antmicro/com-express-7-baseboard/assets/previews/layer1.png

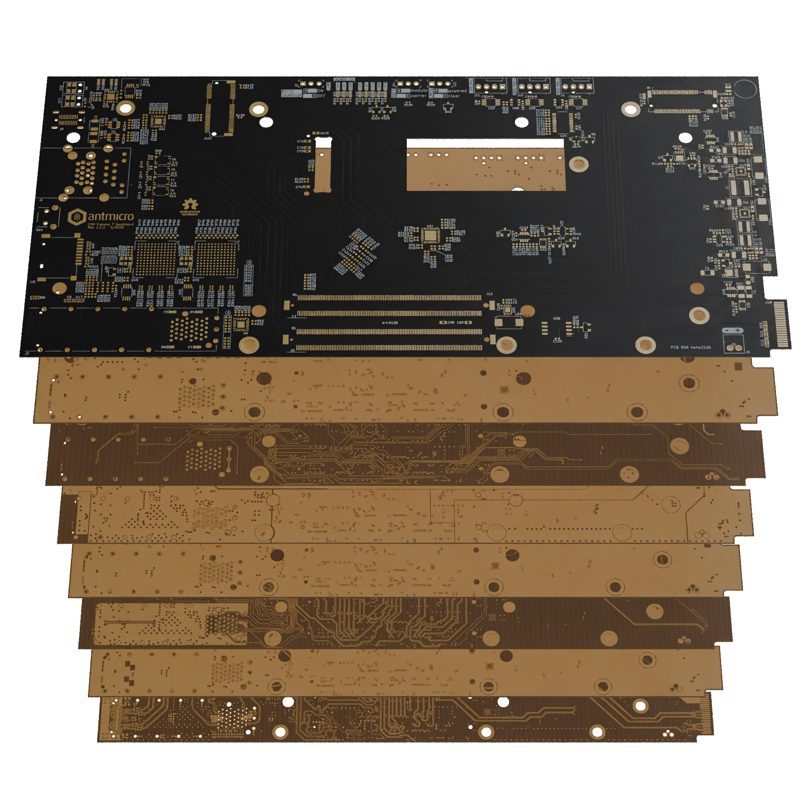
assets/previews/layer1.png
