antmicro/com-express-7-baseboard/assets/previews/layer2.png

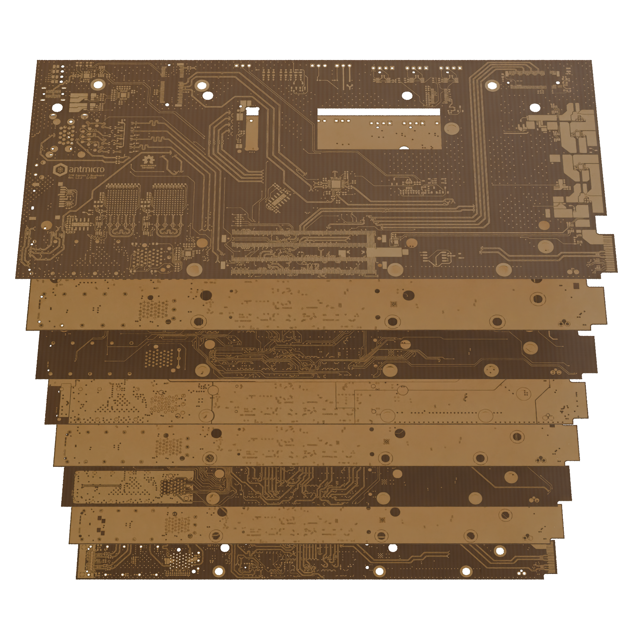
assets/previews/layer2.png
