antmicro/com-express-7-baseboard/assets/previews/layer2.webp

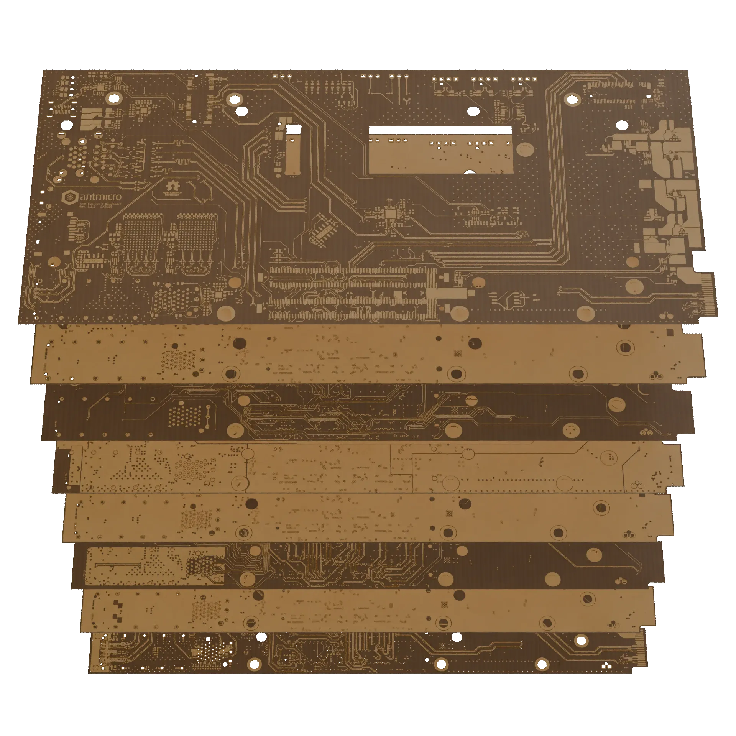
assets/previews/layer2.webp
