antmicro/com-express-7-baseboard/assets/previews/layer2_thumbnail.webp

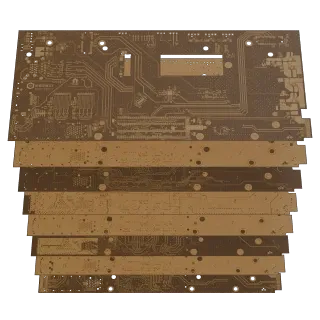
assets/previews/layer2_thumbnail.webp
