antmicro/com-express-7-baseboard/assets/previews/layer3.png

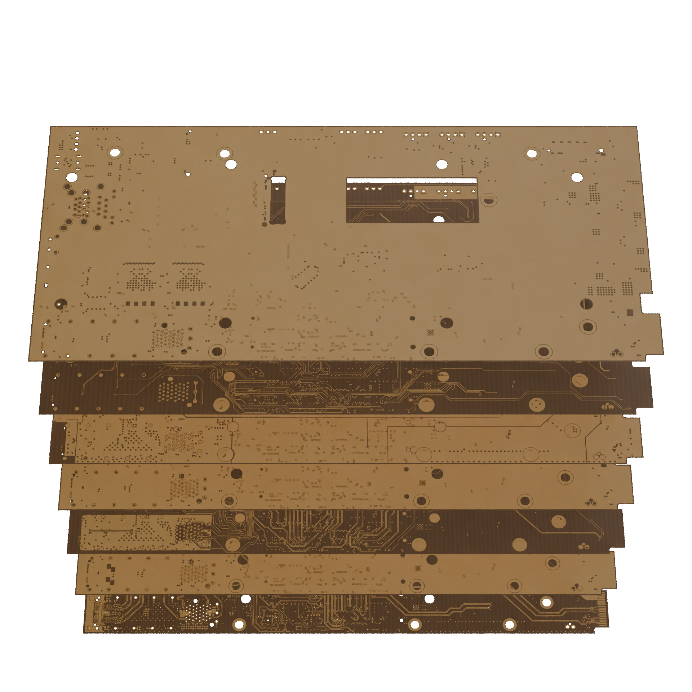
assets/previews/layer3.png
