antmicro/com-express-7-baseboard/assets/previews/layer4.png

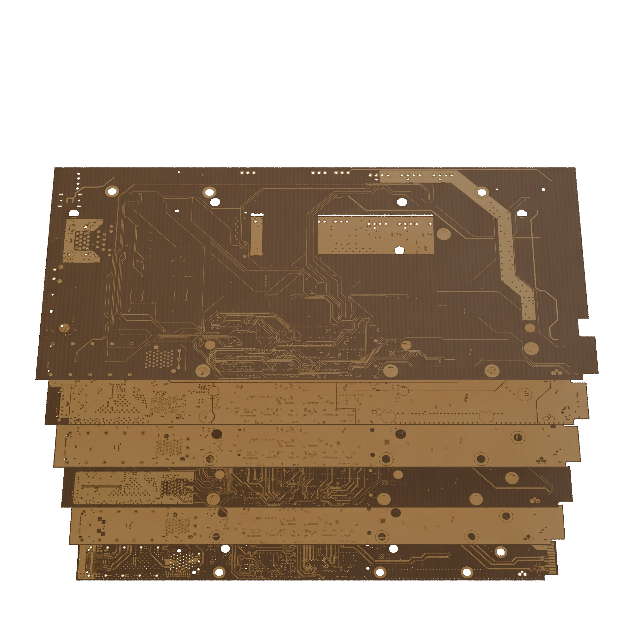
assets/previews/layer4.png
