antmicro/com-express-7-baseboard/assets/previews/layer5.png

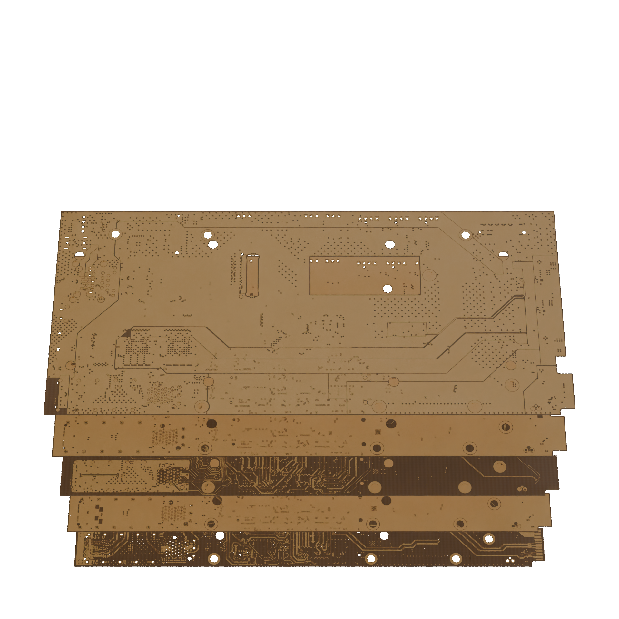
assets/previews/layer5.png
