antmicro/com-express-7-baseboard/assets/previews/layer5.webp

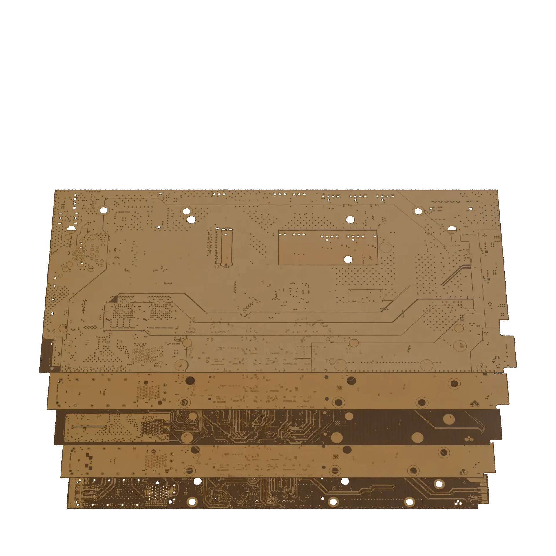
assets/previews/layer5.webp
