antmicro/com-express-7-baseboard/assets/previews/layer5_thumbnail.png

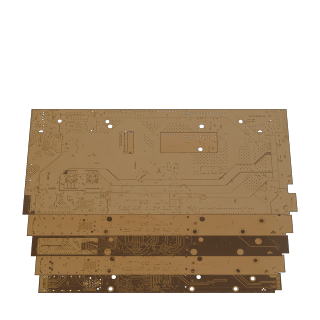
assets/previews/layer5_thumbnail.png
