antmicro/com-express-7-baseboard/assets/previews/layer7.png

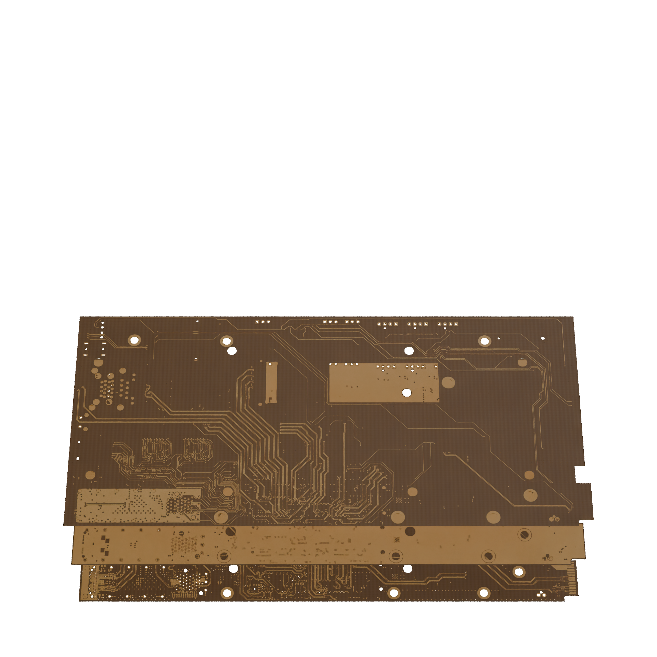
assets/previews/layer7.png
