antmicro/com-express-7-baseboard/assets/previews/layer8.png

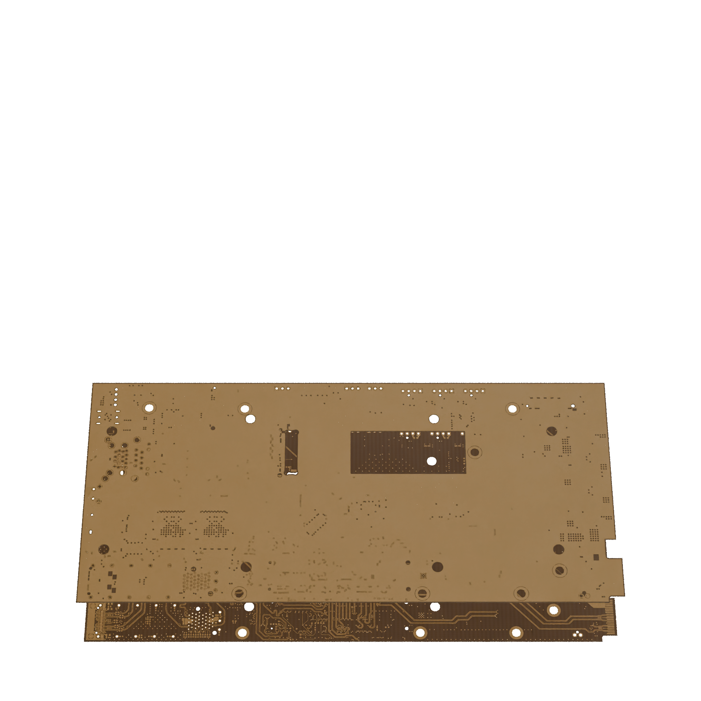
assets/previews/layer8.png
