antmicro/com-express-7-baseboard/assets/previews/layer9.png

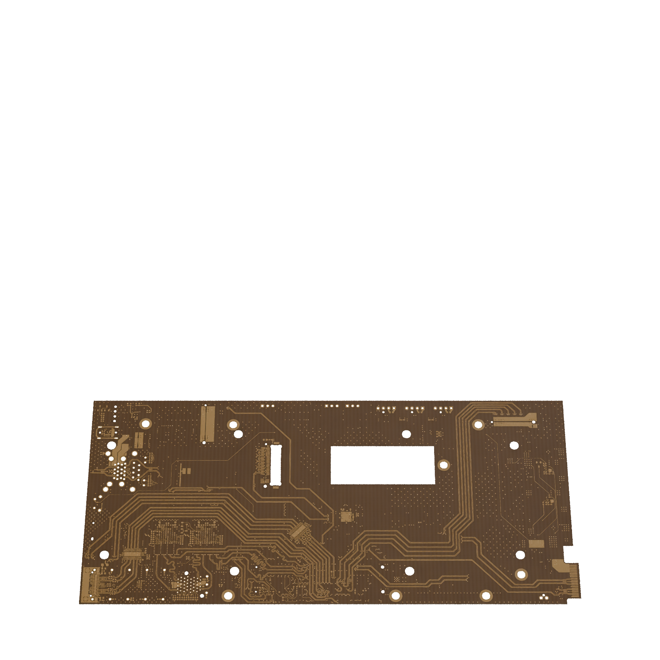
assets/previews/layer9.png
