antmicro/com-express-7-baseboard/assets/previews/leftB.png

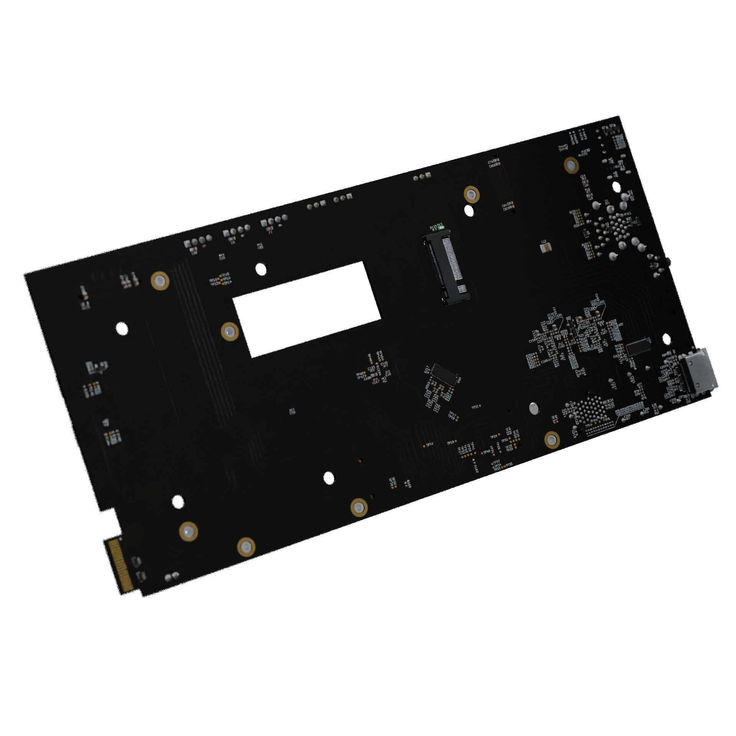
assets/previews/leftB.png
