antmicro/com-express-7-baseboard/assets/previews/leftT.png

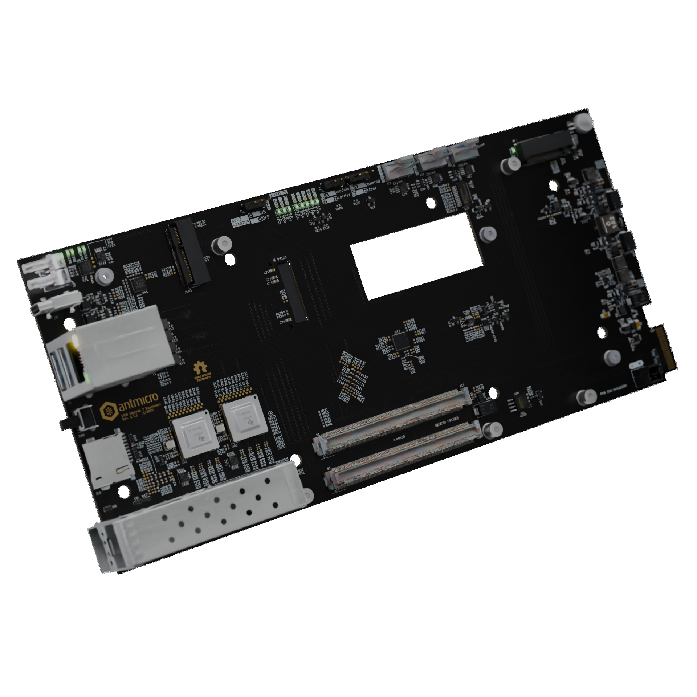
assets/previews/leftT.png
