antmicro/com-express-7-baseboard/assets/previews/orthoB.png

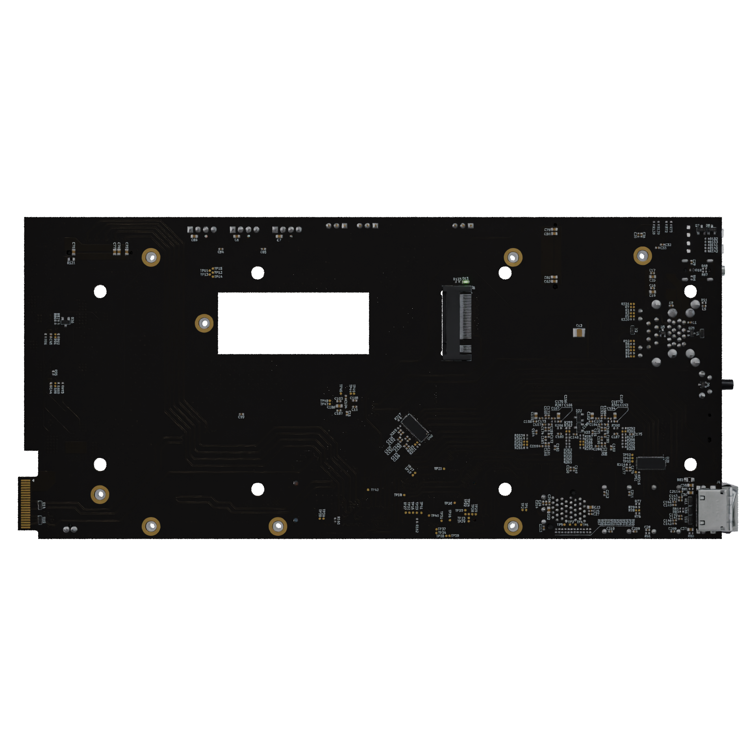
assets/previews/orthoB.png
