antmicro/com-express-7-baseboard/assets/previews/rightB.png

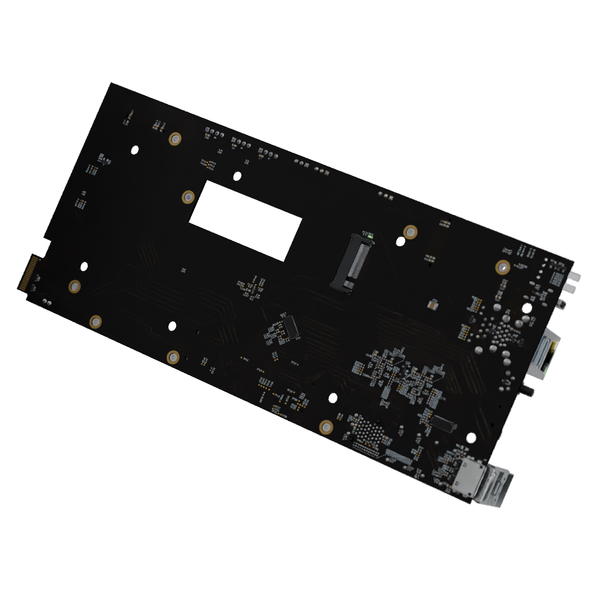
assets/previews/rightB.png
