antmicro/com-express-7-baseboard/assets/previews/rightT.png

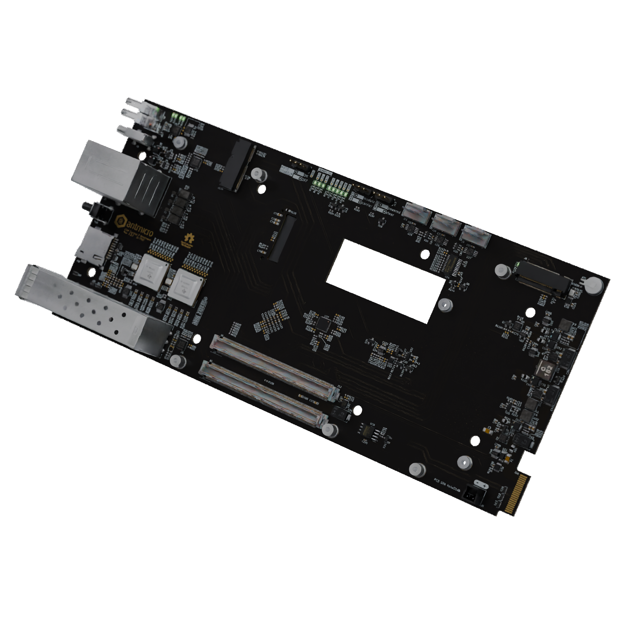
assets/previews/rightT.png
