antmicro/com-express-7-baseboard/assets/wireframe/wireframe_descriptions_bottom.png

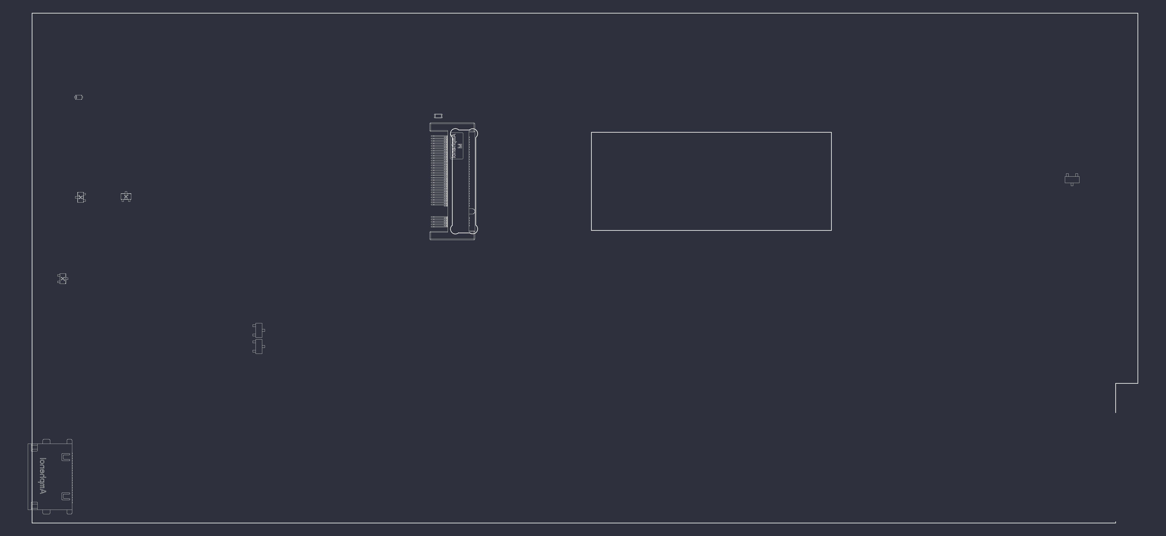
assets/wireframe/wireframe_descriptions_bottom.png
