antmicro/com-express-7-baseboard/assets/wireframe/wireframe_descriptions_top.png

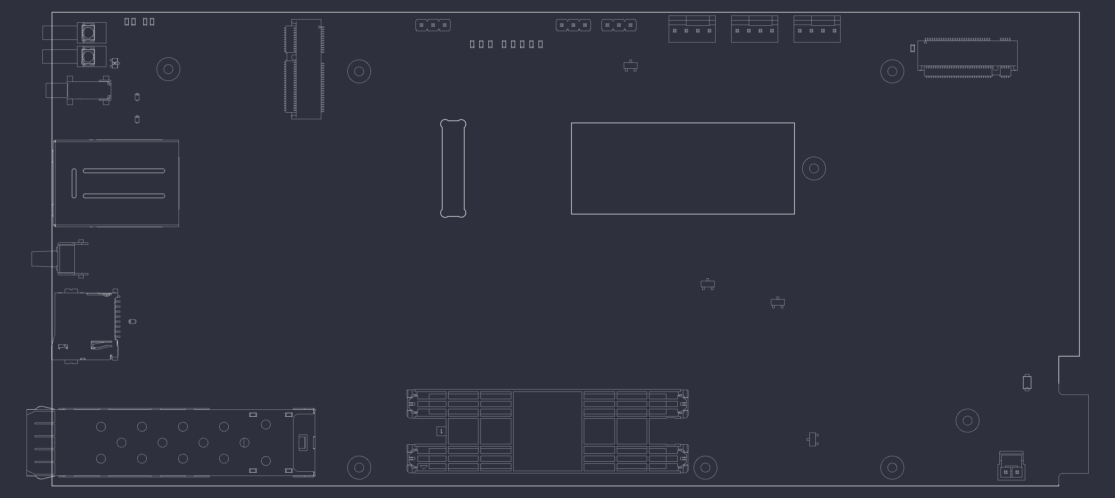
assets/wireframe/wireframe_descriptions_top.png
