antmicro/com-express-7-baseboard/assets/wireframe/wireframe_dimensions.png

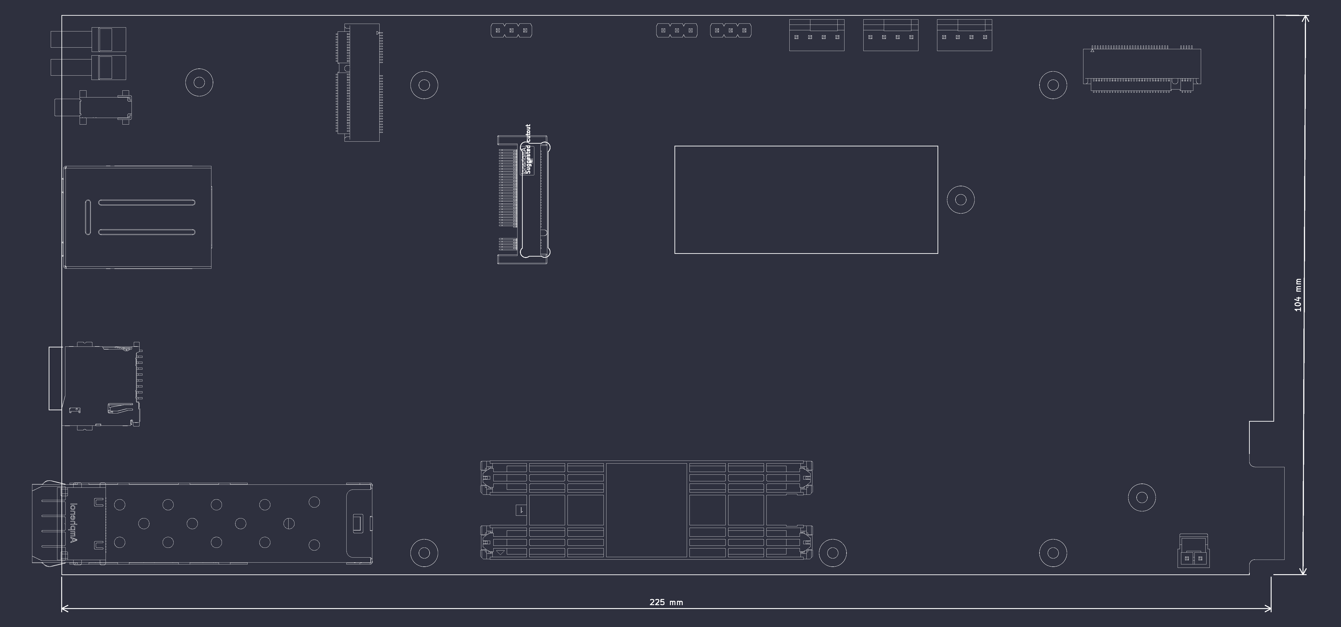
assets/wireframe/wireframe_dimensions.png
