antmicro/com-express-7-baseboard/img/mock.png

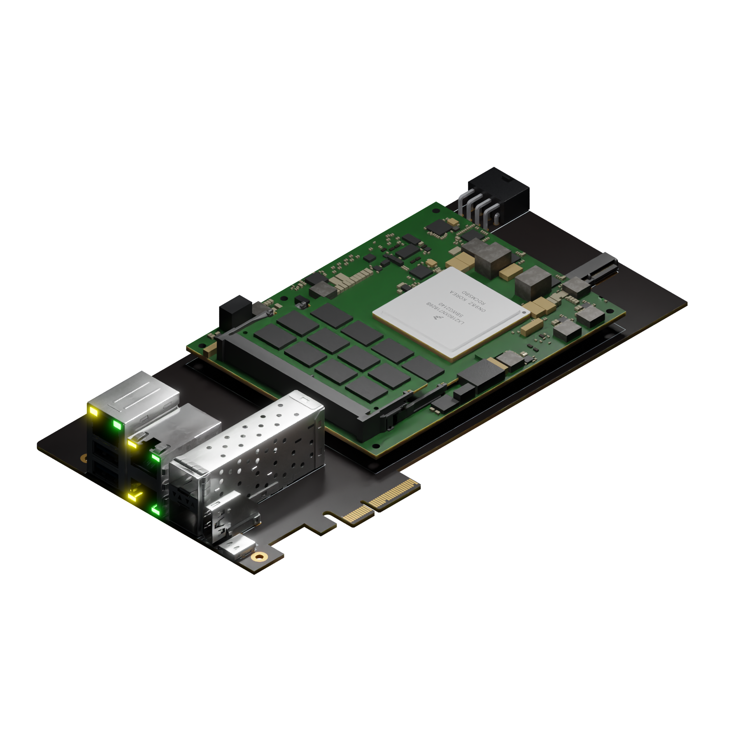
img/mock.png
