antmicro/com-express-7-baseboard/gpio_exp.kicad_sch

## KiCad design gpio_exp.kicad_sch (2025-02-04, an earlier design)

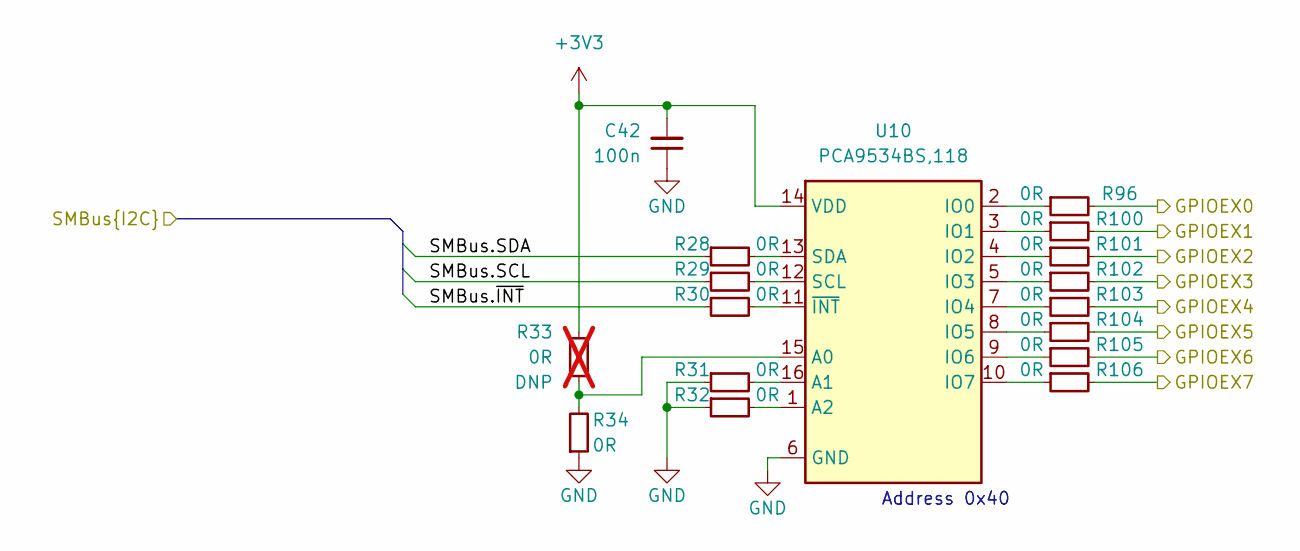
[picture p53: schematic gpio_exp.kicad_sch]

Parts:
C42: C_100n_0402; C_0402_1005Metric; Voltage 50V; MPN GRM155R61H104KE14D
R28, R29, R30, R31, R32, R34, R96, R100, R101, R102, R103, R104, R105, R106: R_0R_0402; R_0402_1005Metric; MPN ERJ2GE0R00X
R33: R_0R_0402; R_0402_1005Metric; MPN ERJ2GE0R00X; not fitted
U10: PCA9534BS_QFN; QFN-16-1EP_4x4mm_P0.65mm; MPN PCA9534BS,118

Connections:
+3V3: C42.2, R33.2, U10.14 (VDD)
GND: C42.1, R31.1, R32.1, R34.1, U10.6 (GND), U10.17 (GND)
GPIOEX0: R96.2
GPIOEX1: R100.2
GPIOEX2: R101.2
GPIOEX3: R102.2
GPIOEX4: R103.2
GPIOEX5: R104.2
GPIOEX6: R105.2
GPIOEX7: R106.2
unnamed: R28.2, U10.13 (SDA)
unnamed: R29.2, U10.12 (SCL)
unnamed: R30.2, U10.11 (~INT)
unnamed: R31.2, U10.16 (A1)
unnamed: R32.2, U10.1 (A2)
unnamed: R33.1, R34.2, U10.15 (A0)
unnamed: R96.1, U10.2 (IO0)
unnamed: R100.1, U10.3 (IO1)
unnamed: R101.1, U10.4 (IO2)
unnamed: R102.1, U10.5 (IO3)
unnamed: R103.1, U10.7 (IO4)
unnamed: R104.1, U10.8 (IO5)
unnamed: R105.1, U10.9 (IO6)
unnamed: R106.1, U10.10 (IO7)
SMBus.SCL: R29.1
SMBus.SDA: R28.1
SMBus.~INT: R30.1

Notes on the sheet:
Address 0x40
