antmicro/com-express-7-baseboard/kr_sfi.kicad_sch

## KiCad design kr_sfi.kicad_sch (2025-02-04, an earlier design)

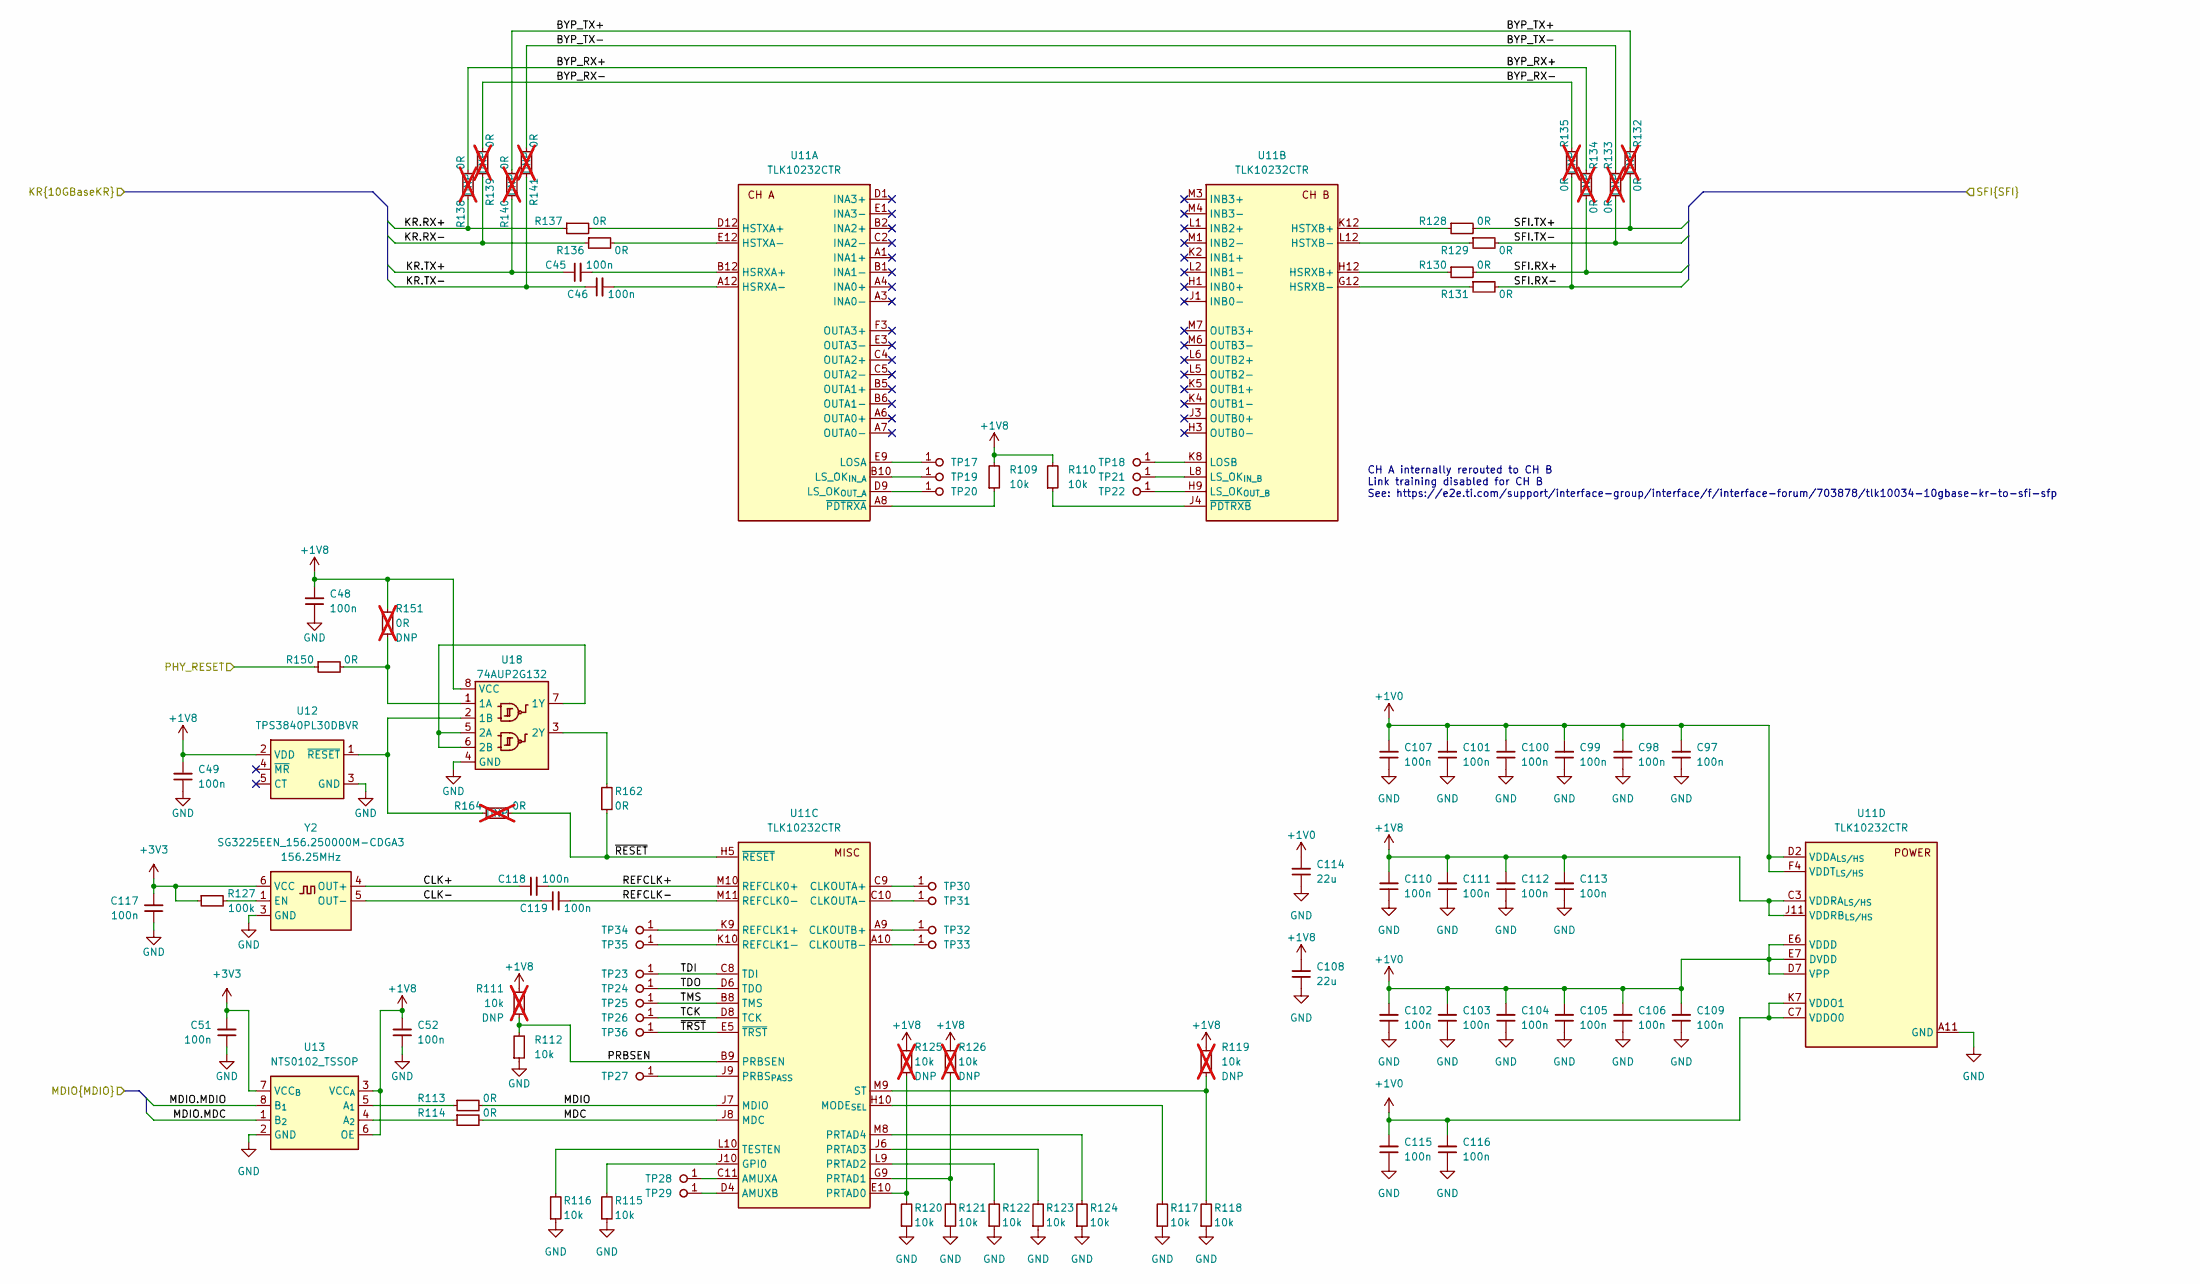
[picture p54: schematic kr_sfi.kicad_sch]

Parts:
C45, C46, C48, C49, C51, C52, C97, C98, C99, C100, C101, C102, C103, C104, C105, C106, C107, C109, C110, C111, C112, C113, C115, C116, C117, C118, C119: C_100n_0402; C_0402_1005Metric; Voltage 50V; MPN GRM155R61H104KE14D
C108, C114: C_22u_0603; C_0603_1608Metric; MPN GRM188R60J226MEA0D
R109, R110, R112, R115, R116, R117, R118, R120, R121, R122, R123, R124: R_10k_0402; R_0402_1005Metric; Tolerance 1%; MPN CR0402-FX-1002GLF
R111, R119, R125, R126: R_10k_0402; R_0402_1005Metric; Tolerance 1%; MPN CR0402-FX-1002GLF; not fitted
R113, R114, R128, R129, R130, R131, R136, R137, R150, R162: R_0R_0402; R_0402_1005Metric; MPN ERJ2GE0R00X
R127: R_100k_0402; R_0402_1005Metric; Tolerance 1%; MPN CR0402-FX-1003GLF
R132, R133, R134, R135, R138, R139, R140, R141, R151, R164: R_0R_0402; R_0402_1005Metric; MPN ERJ2GE0R00X; not fitted
TP17, TP18, TP19, TP20, TP21, TP22, TP23, TP24, TP25, TP26, TP27, TP28, TP29, TP30, TP31, TP32, TP33, TP34, TP35, TP36: TP_0.75mm_SMD; TP_SMD_0.75mm
U11: TLK10232CTR; MPN TLK10232CTR
U12: TPS3840PL30DBVR; SOT-23-5; MPN TPS3840PL30DBVR
U13: NTS0102_TSSOP; TSSOP-8_3x3mm_P0.65mm; MPN NTS0102DP
U18: 74AUP2G132; VSSOP-8_2.3x2mm_P0.5mm; MPN 74AUP2G132
Y2: Oscillator_156.25MHz_SG3225EEN; Oscillator_SMD_Epson_SG3225EEN_3.2x2.5x1.2mm; MPN SG3225EEN_156.250000M-CDGA3

Connections:
+1V0: C97.2, C98.2, C99.2, C100.2, C101.2, C102.2, C103.2, C104.2, C105.2, C106.2, C107.2, C109.2, C114.2, C115.2, C116.2, U11.C7 (VDDO0), U11.D2 (VDDA_{LS/HS}), U11.D7 (VPP), U11.E6 (VDDD), U11.E7 (DVDD), U11.E8 (VDDD), U11.F2 (VDDA_{LS/HS}), U11.F4 (VDDT_{LS/HS}), U11.F6 (VDDD), U11.F7 (DVDD), U11.F9 (VDDT_{LS/HS}), U11.F11 (VDDA_{LS/HS}), U11.G2 (VDDA_{LS/HS}), U11.G4 (VDDT_{LS/HS}), U11.G6 (DVDD), U11.G8 (DVDD), U11.G10 (VDDA_{LS/HS}), U11.H6 (VDDD), U11.H7 (DVDD), U11.H8 (VDDD), U11.J2 (VDDA_{LS/HS}), U11.K7 (VDDO1)
+1V8: C48.2, C49.2, C52.2, C108.2, C110.2, C111.2, C112.2, C113.2, R109.2, R110.2, R111.2, R119.2, R125.2, R126.2, R151.2, U11.C3 (VDDRA_{LS/HS}), U11.E11 (VDDRA_{LS/HS}), U11.J11 (VDDRB_{LS/HS}), U11.K3 (VDDRB_{LS/HS}), U12.2 (VDD), U13.3 (VCC_{A}), U13.6 (OE), U18.8 (VCC)
+3V3: C51.2, C117.2, R127.1, U13.7 (VCC_{B}), Y2.6 (VCC)
BYP_RX+: R134.1, R138.2
BYP_RX-: R135.1, R139.2
BYP_TX+: R132.1, R140.2
BYP_TX-: R133.1, R141.2
CLK+: C118.1, Y2.4 (OUT+)
CLK-: C119.1, Y2.5 (OUT-)
GND: C48.1, C49.1, C51.1, C52.1, C97.1, C98.1, C99.1, C100.1, C101.1, C102.1, C103.1, C104.1, C105.1, C106.1, C107.1, C108.1, C109.1, C110.1, C111.1, C112.1, C113.1, C114.1, C115.1, C116.1, C117.1, R112.1, R115.1, R116.1, R117.1, R118.1, R120.1, R121.1, R122.1, R123.1, R124.1, U11.A2 (GND), U11.A5 (GND), U11.A11 (GND), U11.B3 (GND), U11.B4 (GND), U11.B7 (GND), U11.B11 (GND), U11.C1 (GND), U11.C6 (GND), U11.C12 (GND), U11.D3 (GND), U11.D5 (GND), U11.D10 (GND), U11.D11 (GND), U11.E2 (GND), U11.E4 (GND), U11.F1 (GND), U11.F5 (GND), U11.F8 (GND), U11.F10 (GND), U11.F12 (GND), U11.G1 (GND), U11.G3 (GND), U11.G5 (GND), U11.G7 (GND), U11.G11 (GND), U11.H2 (GND), U11.H4 (GND), U11.H11 (GND), U11.J5 (GND), U11.J12 (GND), U11.K1 (GND), U11.K6 (GND), U11.K11 (GND), U11.L3 (GND), U11.L4 (GND), U11.L7 (GND), U11.L11 (GND), U11.M2 (GND), U11.M5 (GND), U11.M12 (GND), U12.3 (GND), U13.2 (GND), U18.4 (GND), Y2.3 (GND)
KR.RX+: R137.1, R138.1
KR.RX-: R136.1, R139.1
KR.TX+: C45.1, R140.1
KR.TX-: C46.1, R141.1
MDC: R114.2, U11.J8 (MDC)
MDIO: R113.2, U11.J7 (MDIO)
MDIO.MDC: U13.1 (B_{2})
MDIO.MDIO: U13.8 (B_{1})
unnamed: C45.2, U11.B12 (HSRXA+)
unnamed: C46.2, U11.A12 (HSRXA-)
unnamed: R109.1, U11.A8 (~PDTRXA)
unnamed: R110.1, U11.J4 (~PDTRXB)
unnamed: R113.1, U13.5 (A_{1})
unnamed: R114.1, U13.4 (A_{2})
unnamed: R115.2, U11.J10 (GPI0)
unnamed: R116.2, U11.L10 (TESTEN)
unnamed: R117.2, U11.H10 (MODE_{SEL})
unnamed: R118.2, R119.1, U11.M9 (ST)
unnamed: R120.2, R125.1, U11.E10 (PRTAD0)
unnamed: R121.2, R126.1, U11.G9 (PRTAD1)
unnamed: R122.2, U11.L9 (PRTAD2)
unnamed: R123.2, U11.J6 (PRTAD3)
unnamed: R124.2, U11.M8 (PRTAD4)
unnamed: R127.2, Y2.1 (EN)
unnamed: R128.1, U11.K12 (HSTXB+)
unnamed: R129.1, U11.L12 (HSTXB-)
unnamed: R130.1, U11.H12 (HSRXB+)
unnamed: R131.1, U11.G12 (HSRXB-)
unnamed: R136.2, U11.E12 (HSTXA-)
unnamed: R137.2, U11.D12 (HSTXA+)
unnamed: R150.2, R151.1, U18.1 (1A)
unnamed: R162.2, U18.3 (2Y)
unnamed: R164.1, U12.1 (~RESET), U18.2 (1B)
unnamed: TP17.1, U11.E9 (LOSA)
unnamed: TP18.1, U11.K8 (LOSB)
unnamed: TP19.1, U11.B10 (LS_OK_{IN_A})
unnamed: TP20.1, U11.D9 (LS_OK_{OUT_A})
unnamed: TP21.1, U11.L8 (LS_OK_{IN_B})
unnamed: TP22.1, U11.H9 (LS_OK_{OUT_B})
unnamed: TP27.1, U11.J9 (PRBS_{PASS})
unnamed: TP28.1, U11.C11 (AMUXA)
unnamed: TP29.1, U11.D4 (AMUXB)
unnamed: TP30.1, U11.C9 (CLKOUTA+)
unnamed: TP31.1, U11.C10 (CLKOUTA-)
unnamed: TP32.1, U11.A9 (CLKOUTB+)
unnamed: TP33.1, U11.A10 (CLKOUTB-)
unnamed: TP34.1, U11.K9 (REFCLK1+)
unnamed: TP35.1, U11.K10 (REFCLK1-)
unnamed: U18.5 (2A), U18.6 (2B), U18.7 (1Y)
PHY_RESET: R150.1
PRBSEN: R111.1, R112.2, U11.B9 (PRBSEN)
REFCLK+: C118.2, U11.M10 (REFCLK0+)
REFCLK-: C119.2, U11.M11 (REFCLK0-)
SFI.RX+: R130.2, R134.2
SFI.RX-: R131.2, R135.2
SFI.TX+: R128.2, R132.2
SFI.TX-: R129.2, R133.2
TCK: TP26.1, U11.D8 (TCK)
TDI: TP23.1, U11.C8 (TDI)
TDO: TP24.1, U11.D6 (TDO)
TMS: TP25.1, U11.B8 (TMS)
~RESET: R162.1, R164.2, U11.H5 (~RESET)
~TRST: TP36.1, U11.E5 (~TRST)

Notes on the sheet:
CH A internally rerouted to CH B Link training disabled for CH B See: https://e2e.ti.com/support/interface-group/interface/f/interface-forum/703878/tlk10034-10gbase-kr-to-sfi-sfp
