antmicro/com-express-7-baseboard/m2keym_low.kicad_sch

## KiCad design m2keym_low.kicad_sch (2025-02-04, an earlier design)

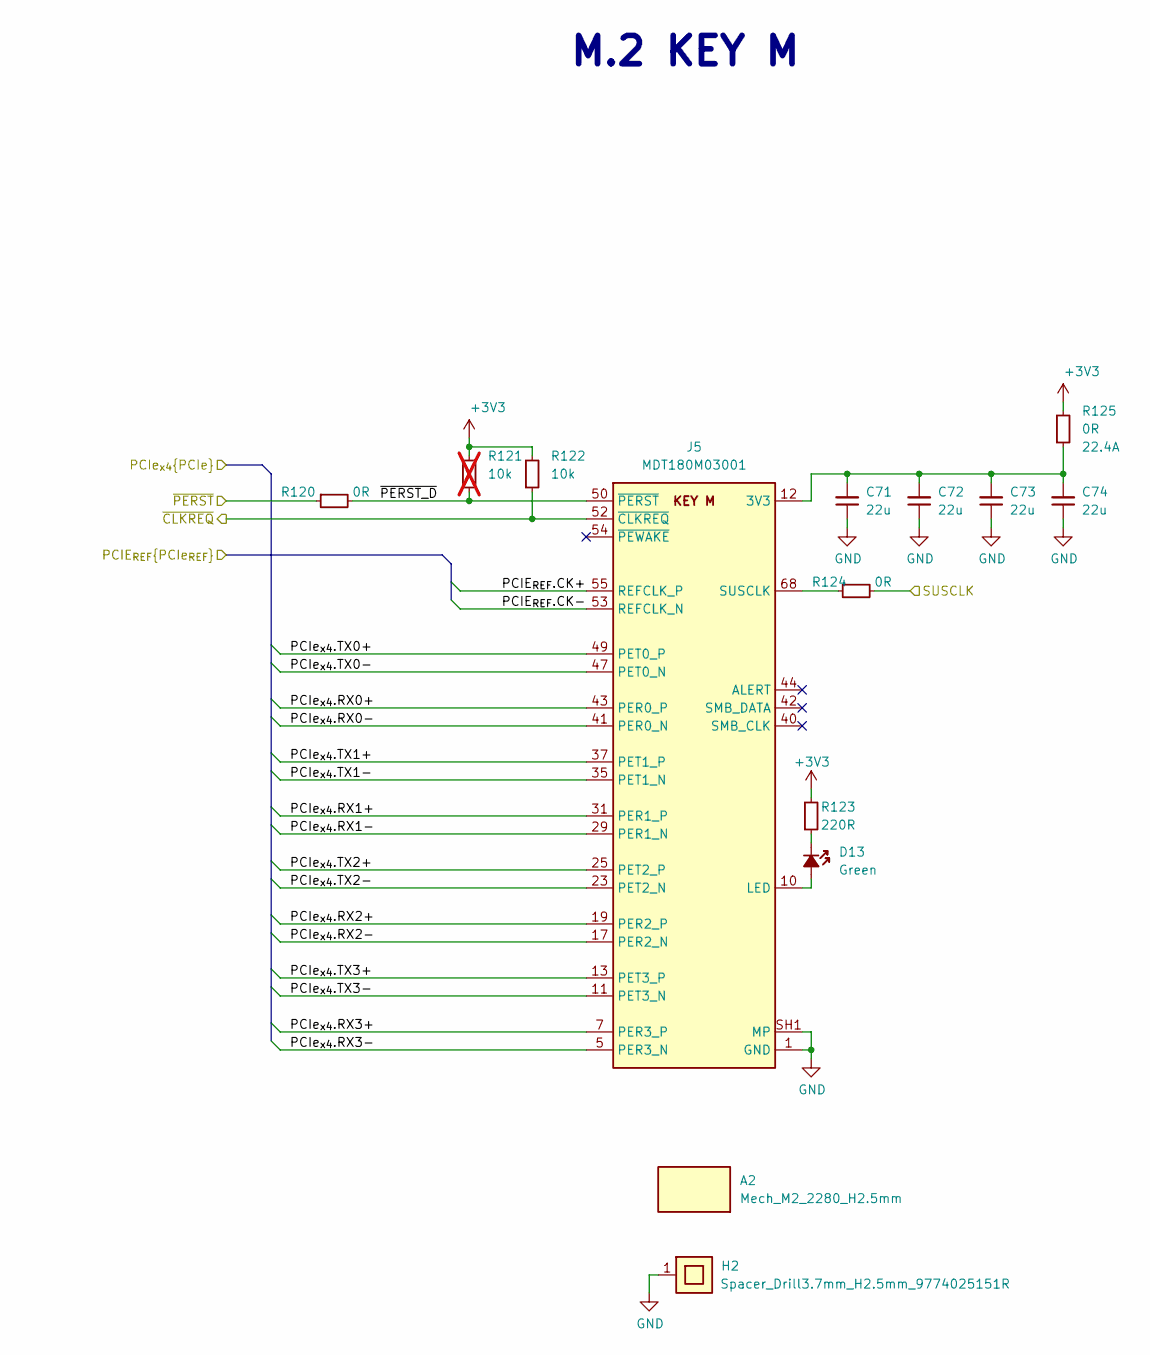
[picture p55: schematic m2keym_low.kicad_sch]

Parts:
A2: Mech_M2_2280_H2.5mm
C71, C72, C73, C74: C_22u_16V_0603; C_0603_1608Metric; Voltage 16V; MPN CL10A226MO7JZNC
D13: LED_G_0603_LTST-C190GKT; LED_0603_1608Metric_G; MPN LTST-C190GKT
H2: Spacer_Drill3.7mm_H2.5mm_9774025151R; MPN 9774025151R
J5: Bus_M.2_MDT180M03001; Bus_M.2_Socket_Key_M_Amphenol_MDT180M03001; MPN MDT180M03001
R120, R124: R_0R_0402; R_0402_1005Metric; MPN ERJ2GE0R00X
R121: R_10k_0402; R_0402_1005Metric; Tolerance 1%; MPN CR0402-FX-1002GLF; not fitted
R122: R_10k_0402; R_0402_1005Metric; Tolerance 1%; MPN CR0402-FX-1002GLF
R123: R_220R_0402; R_0402_1005Metric; Tolerance 1%; MPN CR0402-FX-2200GLF
R125: R_0R_22.4A_0603; R_0603_1608Metric; Tolerance template_tolerance; MPN PMR03EZPJ000

Connections:
+3V3: R121.2, R122.2, R123.2, R125.2
GND: C71.1, C72.1, C73.1, C74.1, H2.1, J5.1 (GND), J5.3 (GND), J5.9 (GND), J5.15 (GND), J5.21 (GND), J5.27 (GND), J5.33 (GND), J5.39 (GND), J5.45 (GND), J5.51 (GND), J5.57 (GND), J5.71 (GND), J5.73 (GND), J5.75 (GND), J5.SH1 (MP), J5.SH2 (MP)
unnamed: C71.2, C72.2, C73.2, C74.2, J5.2 (3V3), J5.4 (3V3), J5.12 (3V3), J5.14 (3V3), J5.16 (3V3), J5.18 (3V3), J5.70 (3V3), J5.72 (3V3), J5.74 (3V3), R125.1
unnamed: D13.1 (C), R123.1
unnamed: D13.2 (A), J5.10 (LED)
unnamed: J5.68 (SUSCLK), R124.1
PCIE_{REF}.CK+: J5.55 (REFCLK_P)
PCIE_{REF}.CK-: J5.53 (REFCLK_N)
PCIe_{x4}.RX0+: J5.43 (PER0_P)
PCIe_{x4}.RX0-: J5.41 (PER0_N)
PCIe_{x4}.RX1+: J5.31 (PER1_P)
PCIe_{x4}.RX1-: J5.29 (PER1_N)
PCIe_{x4}.RX2+: J5.19 (PER2_P)
PCIe_{x4}.RX2-: J5.17 (PER2_N)
PCIe_{x4}.RX3+: J5.7 (PER3_P)
PCIe_{x4}.RX3-: J5.5 (PER3_N)
PCIe_{x4}.TX0+: J5.49 (PET0_P)
PCIe_{x4}.TX0-: J5.47 (PET0_N)
PCIe_{x4}.TX1+: J5.37 (PET1_P)
PCIe_{x4}.TX1-: J5.35 (PET1_N)
PCIe_{x4}.TX2+: J5.25 (PET2_P)
PCIe_{x4}.TX2-: J5.23 (PET2_N)
PCIe_{x4}.TX3+: J5.13 (PET3_P)
PCIe_{x4}.TX3-: J5.11 (PET3_N)
SUSCLK: R124.2
~CLKREQ: J5.52 (~CLKREQ), R122.1
~PERST_D: J5.50 (~PERST), R120.2, R121.1
~PERST: R120.1

Notes on the sheet:
M.2 KEY M
