antmicro/com-express-7-baseboard/sd_card.kicad_sch

## KiCad design sd_card.kicad_sch (2025-02-04, an earlier design)

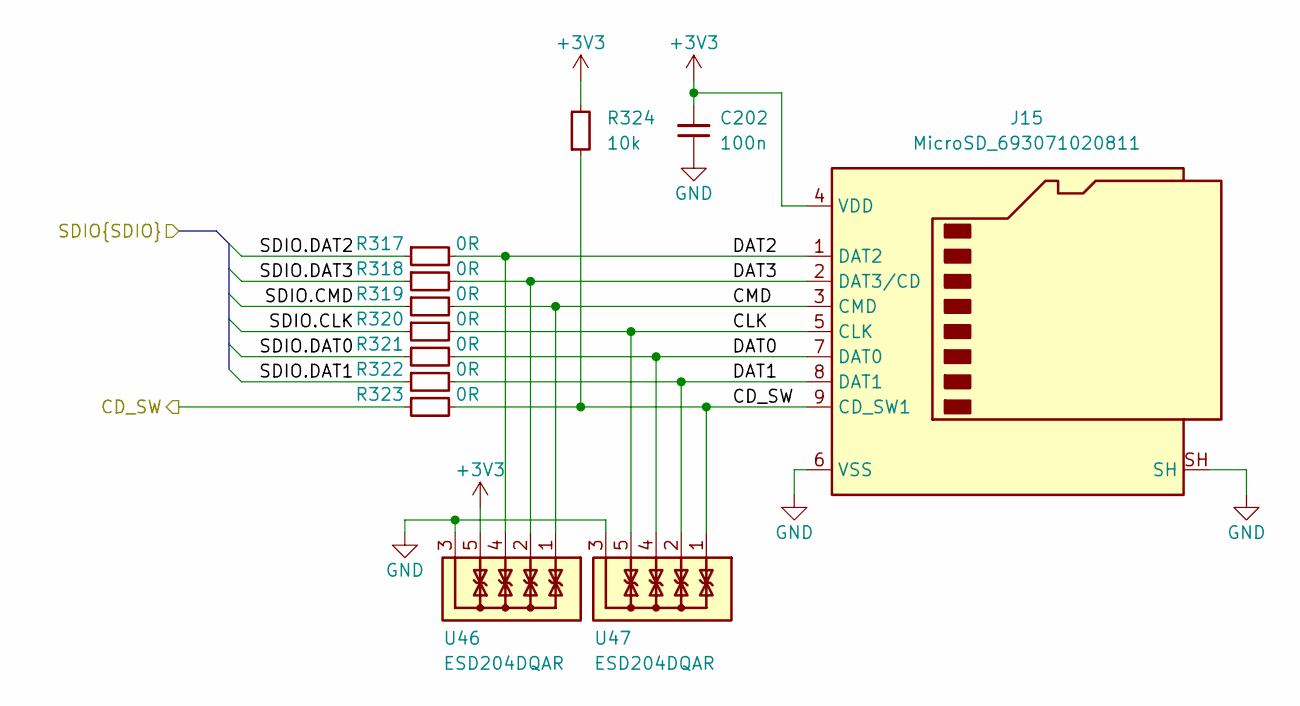
[picture p56: schematic sd_card.kicad_sch]

Parts:
C202: C_100n_0402; C_0402_1005Metric; Voltage 50V; MPN GRM155R61H104KE14D
J15: MicroSD_693071020811; MicroSD_Wurth_693071020811; MPN 693071020811
R317, R318, R319, R320, R321, R322, R323: R_0R_0402; R_0402_1005Metric; MPN ERJ2GE0R00X
R324: R_10k_0402; R_0402_1005Metric; Tolerance 1%; MPN CR0402-FX-1002GLF
U46, U47: ESD204DQAR; USON-10_2.5x1mm_P0.5mm; MPN ESD204DQAR

Connections:
+3V3: C202.2, J15.4 (VDD), R324.2, U46.5, U46.6
CD_SW: J15.9 (CD_SW1), R323.1, R323.2, R324.1, U47.1, U47.10
CLK: J15.5 (CLK), R320.2, U47.5, U47.6
CMD: J15.3 (CMD), R319.2, U46.1, U46.10
DAT0: J15.7 (DAT0), R321.2, U47.4, U47.7
DAT1: J15.8 (DAT1), R322.2, U47.2, U47.9
DAT2: J15.1 (DAT2), R317.2, U46.4, U46.7
DAT3: J15.2 (DAT3/CD), R318.2, U46.2, U46.9
GND: C202.1, J15.6 (VSS), J15.SH, U46.3, U46.8, U47.3, U47.8
SDIO.CLK: R320.1
SDIO.CMD: R319.1
SDIO.DAT0: R321.1
SDIO.DAT1: R322.1
SDIO.DAT2: R317.1
SDIO.DAT3: R318.1
